redstoner-35/XTRLaser/Firmware/include/Logic/SelfTest.h

#ifndef _SelfTest_
#define _SelfTest_

//错误类型枚举
typedef enum
	{
	Fault_None,    //没有错误发生
	Fault_DCDCFailedToStart, //DCDC无法启动 ID:1
	Fault_DCDCShort, //DCDC输出短路  ID:2
	Fault_InputOVP, //输入过压保护 ID:3
	Fault_DCDCOpen,  //LED开路 ID:4
	Fault_NTCFailed, //NTC故障 ID:5
	Fault_OverHeat, //过热故障 ID:6
	Fault_RampConfigError,     //系统无法找到无极调光配置 ID:7
	}FaultCodeDef;	

//外部引用
extern xdata FaultCodeDef ErrCode; //错误代码
	
//函数
void ReportError(FaultCodeDef Code); //报告错误
void ClearError(void); //消除错误
void DisplayErrorTIMHandler(void); //显示错误时候用到的计时器处理
void DisplayErrorIDHandler(void); //根据错误ID进行显示的处理
void OutputFaultDetect(void); //输出故障监测函数	
bit IsErrorFatal(void);	//查询错误是否致命
	
#endif
